EmperorSmith/HomePowerBank/hardware/lv_power/lv_backup/LTC3106.asc

C1: cap; 4.7µ; Rser=1m
C2: cap; 22µ; Rser=1m
C3: cap; 1; Rser=1m
C4: cap; 22µ; Rser=1m
C5: cap; 4.7µ; Rser=1m
C6: cap; 22µ; Rser=1m
C7: cap; 22µ; Rser=1m
C8: cap; 100n; Rser=1m
D1: diode; BAT54
L1: ind; 10µ; Rser=30m
R1: res; 500
R3: res; 80k
R4: res; 20k
R5: res; 100k
U1: LTC3106
V1: voltage; PULSE(5 0 10m 5n 5n 10m 2); Rser=80m
V2: voltage; 2.5
Named nets: 0, OUT, IN, BAT, VCC, AUX, SW1, SW2, PG
.ic V(BAT)=3 V(OUT)=4.5
.tran 2
