EmperorSmith/HomePowerBank/hardware/lv_power/lv_stepup/step_up.asc

C1: cap; 4.7µ; Rser=1m
C2: cap; 3µ; Rser=1m
C3: cap; 3µ; Rser=1m
C4: cap; 3µ; Rser=1m
C5: cap; 3µ; Rser=1m
C6: cap; 3k; Rser=50m
D1: diode; MBRS1100
L1: ind; 28µ; Rser=.23
L2: ind; 252µ; Rser=1.44
R1: res; 180k
R2: res; 100k
U1: LT8301
V1: voltage; 5; Rser=100m
V2: voltage; PULSE(0 5 10m 5n 5n 100m 1)
Named nets: 0, SUP, SW, OUT, SEC, EN
K1 L1 L2 1
.ic V(OUT)=40
.tran 130m
