EmperorSmith/HomePowerBank/hardware/lv_power/usb_interface/bus_switch.asc

C1: cap; 15µ; Rser=1m
C2: cap; 10n; Rser=1m
C3: cap; 2.2µ; Rser=1m
M1: pmos; RRL035P03
M2: pmos; RRL035P03
M3: nmos; 2N7002
R1: res; 1Meg
R2: res; 100k
R3: res; 5
V1: voltage; PULSE(0 3.3 1m 5n 5n 100m 200m)
V2: voltage; 5; Rser=50m
Named nets: 0, TRG, SRC, DEST
.tran 300m
