EmperorSmith/HomePowerBank/software/HomePowerBank/CellMon.h

#ifndef _CELLMON_H
#define _CELLMON_H


// cell monitor SPI port definition
#define CELL_SPI_PORT spi0
#define PIN_C_CIPO 4
#define PIN_C_CS   5
#define PIN_C_SCK  6
#define PIN_C_COPI 7


int CellMonInit();


#endif
