EmperorSmith/HomePowerBank/software/HomePowerBank/PackMon.h

#ifndef _PACKMON_H
#define _PACKMON_H

// pack monitor SPI port definition
#define PACK_SPI_PORT spi1
#define PIN_P_CIPO 8
#define PIN_P_CS 9
#define PIN_P_SCK 10
#define PIN_P_COPI 11

int PackMonInit();



#endif
